ariag713/Mono-Cycle/schematics/Monocycle1.5/ECET_430_Monocycle_project.kicad_sch

## KiCad design schematics/Monocycle1.5/ECET_430_Monocycle_project.kicad_sch (2024-10-30)

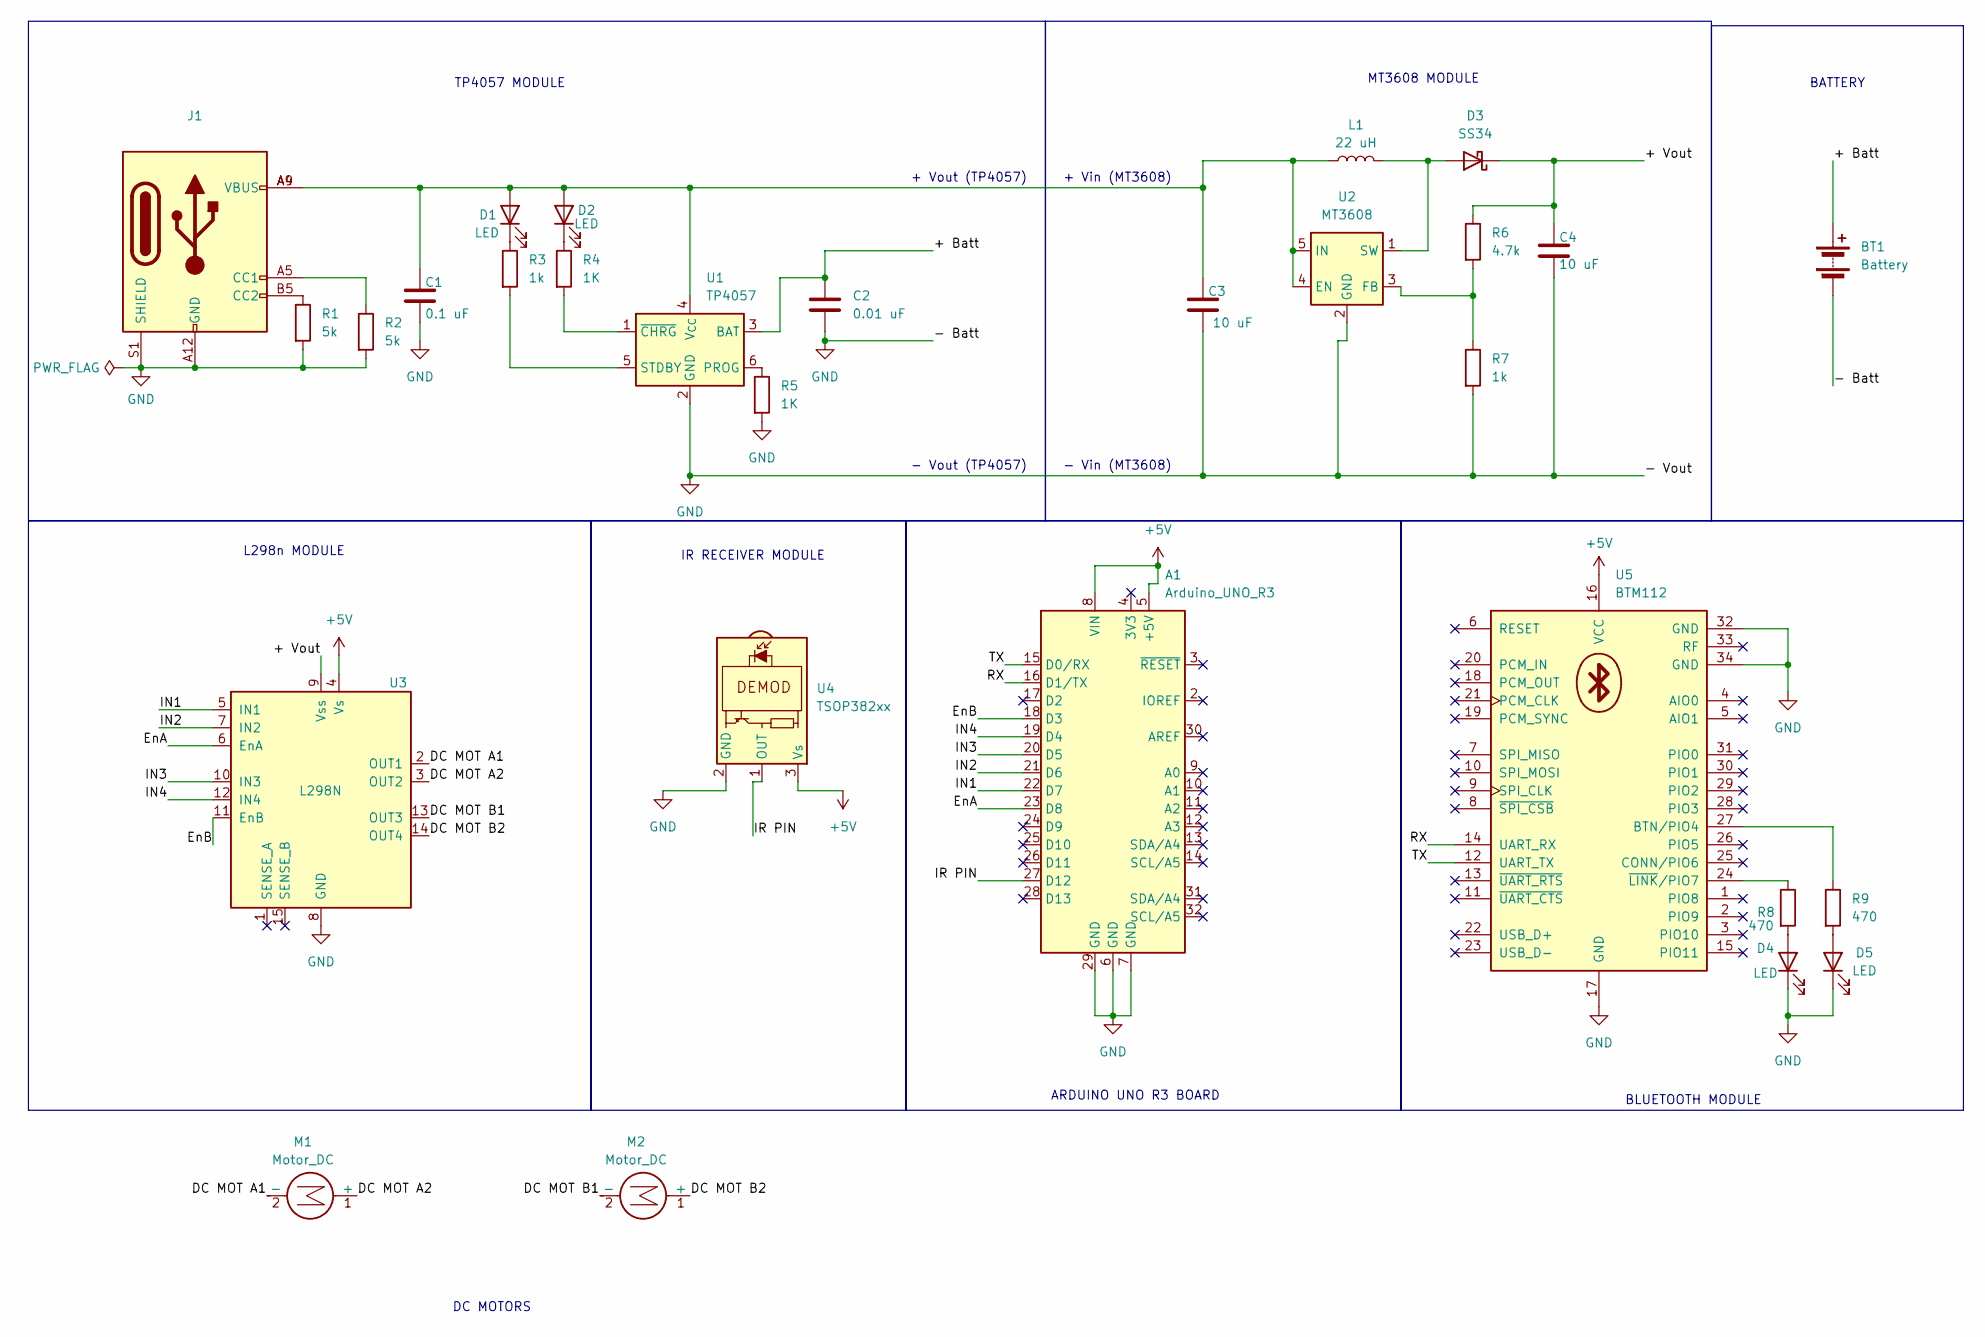
[picture p5: schematic ECET_430_Monocycle_project.kicad_sch]

Parts:
A1: Arduino_UNO_R3
BT1: Battery
C1: 0.1 uF; C_0805_2012Metric_Pad1.18x1.45mm_HandSolder
C2: 0.01 uF
C3, C4: 10 uF; C_0805_2012Metric_Pad1.18x1.45mm_HandSolder
D1, D2, D4, D5: LED; LED_0805_2012Metric_Pad1.15x1.40mm_HandSolder
D3: SS34; D_SMA
J1: USB_C_Receptacle_PowerOnly_24P
L1: 22 uH
M1, M2: Motor_DC
R1, R2: 5k; R_0805_2012Metric_Pad1.20x1.40mm_HandSolder
R3, R7: 1k; R_0805_2012Metric_Pad1.20x1.40mm_HandSolder
R4, R5: 1K; R_0805_2012Metric_Pad1.20x1.40mm_HandSolder
R6: 4.7k; R_0805_2012Metric_Pad1.20x1.40mm_HandSolder
R8, R9: 470; R_0805_2012Metric_Pad1.20x1.40mm_HandSolder
U1: TP4057; TSOT-23-5
U2: MT3608; SOT-23-6
U3: L298N; TO-220-15_P2.54x2.54mm_StaggerOdd_Lead4.58mm_Vertical
U4: TSOP382xx; Vishay_MINICAST-3Pin
U5: BTM112

Connections:
+5V: A1.5 (+5V), A1.8 (VIN), U3.4 (Vs), U4.3 (Vs), U5.16 (VCC)
+ Batt: BT1.1 (+), C2.1, U1.3 (BAT)
+ Vout: C4.1, D3.1 (K), R6.1, U3.9 (Vss)
DC MOT A1: M1.2 (-), U3.2 (OUT1)
DC MOT A2: M1.1 (+), U3.3 (OUT2)
DC MOT B1: M2.2 (-), U3.13 (OUT3)
DC MOT B2: M2.1 (+), U3.14 (OUT4)
EnA: A1.23 (D8), U3.6 (EnA)
EnB: A1.18 (D3), U3.11 (EnB)
GND: A1.6 (GND), A1.7 (GND), A1.29 (GND), BT1.2 (-), C1.2, C2.2, C3.2, C4.2, D4.1 (K), D5.1 (K), J1.A1 (GND), J1.A12 (GND), J1.B1 (GND), J1.B12 (GND), J1.S1 (SHIELD), R1.2, R2.2, R5.2, R7.2, U1.2 (GND), U2.2 (GND), U3.8 (GND), U4.2 (GND), U5.17 (GND), U5.32 (GND), U5.34 (GND)
IN1: A1.22 (D7), U3.5 (IN1)
IN2: A1.21 (D6), U3.7 (IN2)
IN3: A1.20 (D5), U3.10 (IN3)
IN4: A1.19 (D4), U3.12 (IN4)
IR PIN: A1.27 (D12), U4.1 (OUT)
unnamed: C1.1, C3.1, D1.2 (A), D2.2 (A), J1.A4 (VBUS), J1.A9 (VBUS), J1.B4 (VBUS), J1.B9 (VBUS), L1.1, U1.4 (V_{CC}), U2.4 (EN), U2.5 (IN)
unnamed: D1.1 (K), R3.1
unnamed: D2.1 (K), R4.1
unnamed: D3.2 (A), L1.2, U2.1 (SW)
unnamed: D4.2 (A), R8.2
unnamed: D5.2 (A), R9.2
unnamed: J1.A5 (CC1), R2.1
unnamed: J1.B5 (CC2), R1.1
unnamed: R3.2, U1.5 (STDBY)
unnamed: R4.2, U1.1 (~CHRG)
unnamed: R5.1, U1.6 (PROG)
unnamed: R6.2, R7.1, U2.3 (FB)
unnamed: R8.1, U5.24 (~LINK/PIO7)
unnamed: R9.1, U5.27 (BTN/PIO4)
RX: A1.16 (D1/TX), U5.14 (UART_RX)
TX: A1.15 (D0/RX), U5.12 (UART_TX)

Notes on the sheet:
ARDUINO UNO R3 BOARD
DC MOTORS
TP4057 MODULE
+ Vout (TP4057)
- Vout (TP4057)
MT3608 MODULE
IR RECEIVER MODULE
BATTERY
BLUETOOTH MODULE
- Vin (MT3608)
+ Vin (MT3608)
L298n MODULE
