ariag713/Mono-Cycle/schematics/v1.0/Remote_Controller_Schematic.kicad_sch

## KiCad design schematics/v1.0/Remote_Controller_Schematic.kicad_sch (2024-09-24)

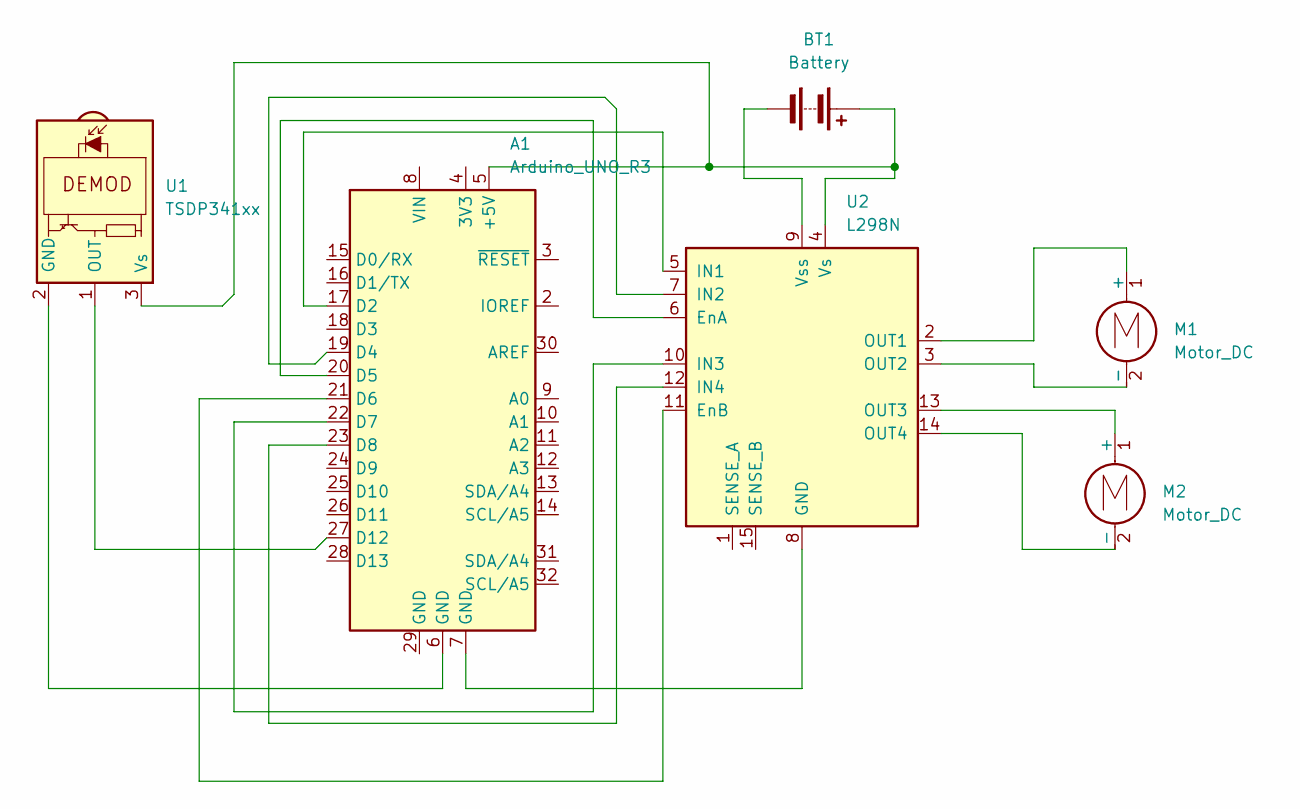
[picture p6: schematic Remote_Controller_Schematic.kicad_sch]

Parts:
A1: Arduino_UNO_R3
BT1: Battery
M1, M2: Motor_DC
U1: TSDP341xx; Vishay_MOLD-3Pin
U2: L298N; TO-220-15_P2.54x2.54mm_StaggerOdd_Lead4.58mm_Vertical

Connections:
unnamed: A1.5 (+5V), BT1.1 (+), U1.3 (Vs), U2.4 (Vs)
unnamed: A1.6 (GND), U1.2 (GND)
unnamed: A1.7 (GND), U2.8 (GND)
unnamed: A1.17 (D2), U2.5 (IN1)
unnamed: A1.19 (D4), U2.7 (IN2)
unnamed: A1.20 (D5), U2.6 (EnA)
unnamed: A1.21 (D6), U2.11 (EnB)
unnamed: A1.22 (D7), U2.10 (IN3)
unnamed: A1.23 (D8), U2.12 (IN4)
unnamed: A1.27 (D12), U1.1 (OUT)
unnamed: BT1.2 (-), U2.9 (Vss)
unnamed: M1.1 (+), U2.2 (OUT1)
unnamed: M1.2 (-), U2.3 (OUT2)
unnamed: M2.1 (+), U2.13 (OUT3)
unnamed: M2.2 (-), U2.14 (OUT4)
